larshasstdas/4x5-Makropad-with-433Mhz-transmitter/Daemon/config.py

import json
import os

CONFIG_PATH = os.path.join(os.path.dirname(__file__), "config.json")

def load_config():
    with open(CONFIG_PATH, "r", encoding="utf-8") as f:
        return json.load(f)
    
def write_config(config):
    with open(CONFIG_PATH, "w", encoding="utf-8") as f:
        json.dump(config, f, indent=2, ensure_ascii=False)
    
        
        
